AleDelMen/Aquaculture-IoT-device/WebServer/dist/img/boxed-bg.jpg

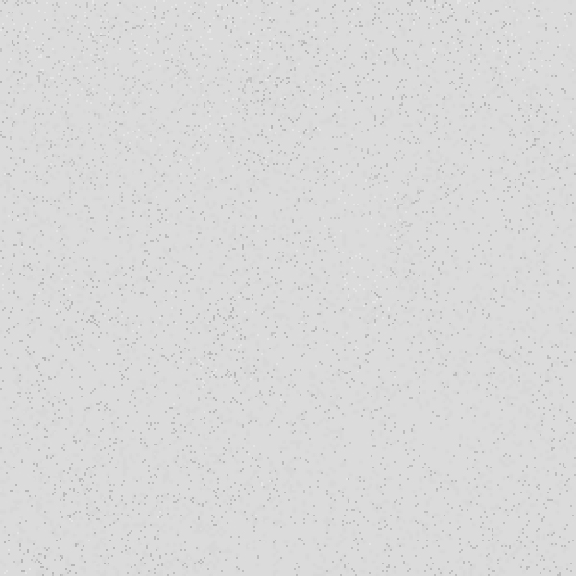
WebServer/dist/img/boxed-bg.jpg
