AleDelMen/Aquaculture-IoT-device/WebServer/dist/img/default-150x150.png

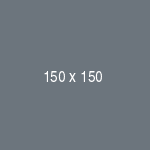
WebServer/dist/img/default-150x150.png
