AleDelMen/Aquaculture-IoT-device/WebServer/dist/img/photo1.png

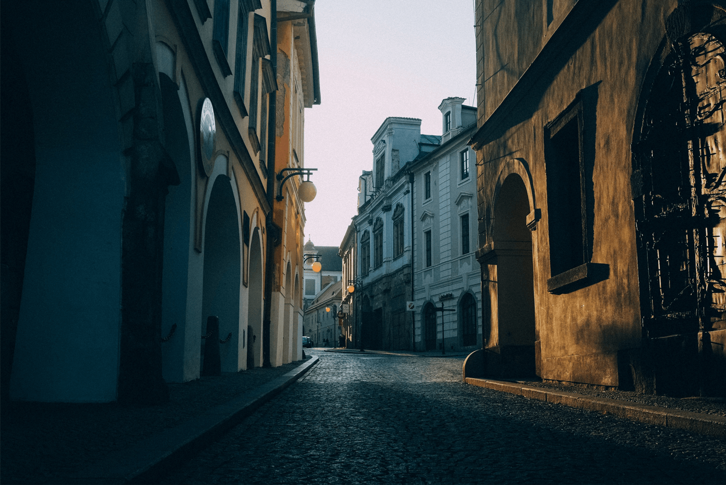
WebServer/dist/img/photo1.png
