AleDelMen/Aquaculture-IoT-device/WebServer/dist/img/photo2.png

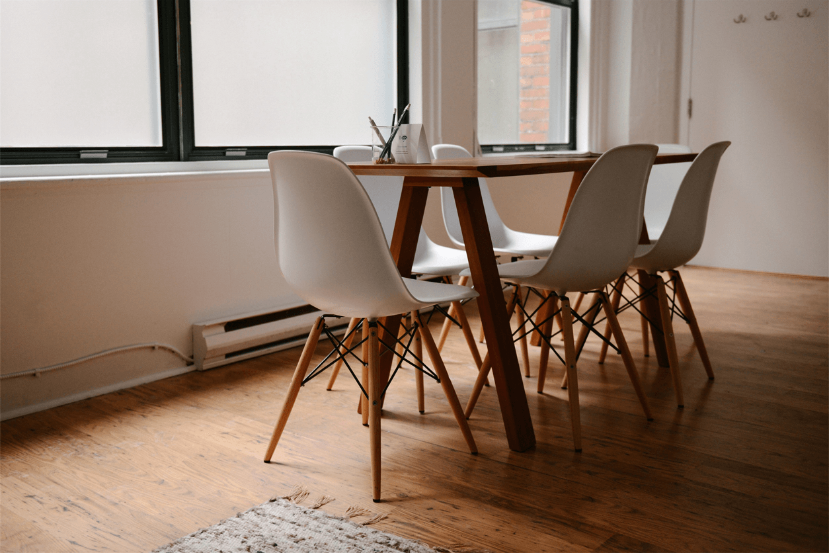
WebServer/dist/img/photo2.png
