AleDelMen/Aquaculture-IoT-device/WebServer/dist/img/photo3.jpg

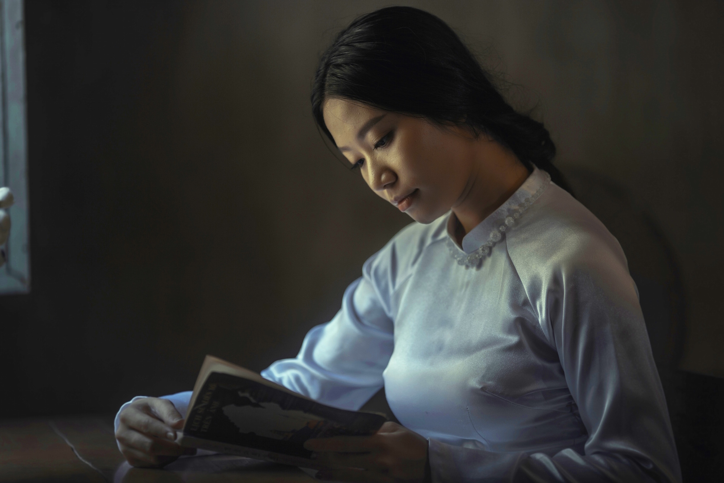
WebServer/dist/img/photo3.jpg
