AleDelMen/Aquaculture-IoT-device/WebServer/dist/img/photo4.jpg

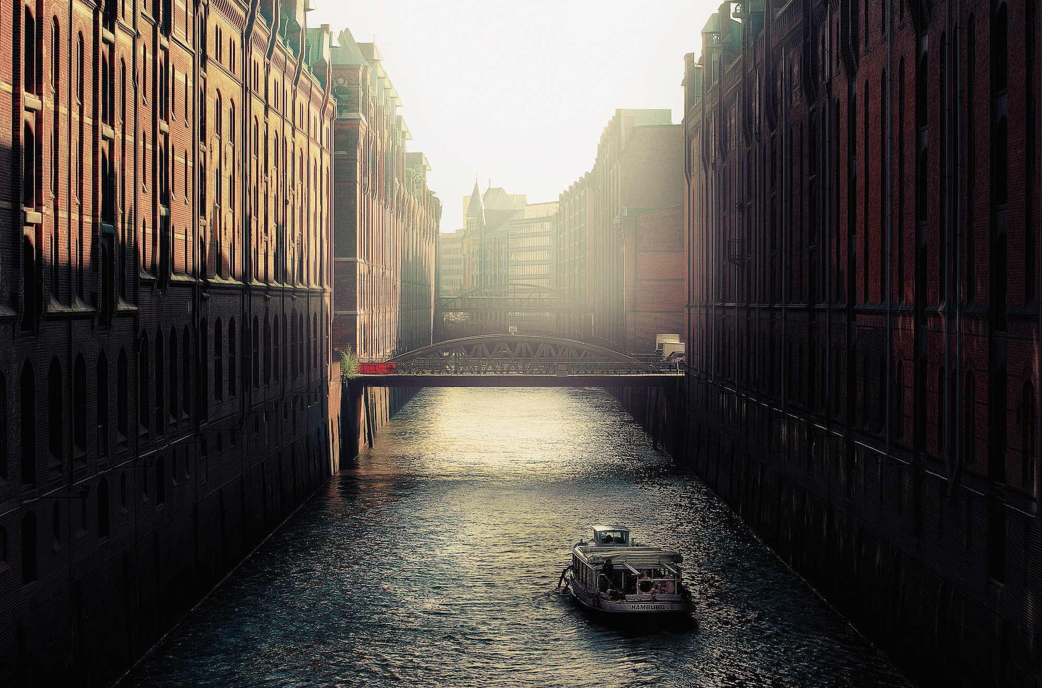
WebServer/dist/img/photo4.jpg
