AleDelMen/Aquaculture-IoT-device/WebServer/dist/img/prod-1.jpg

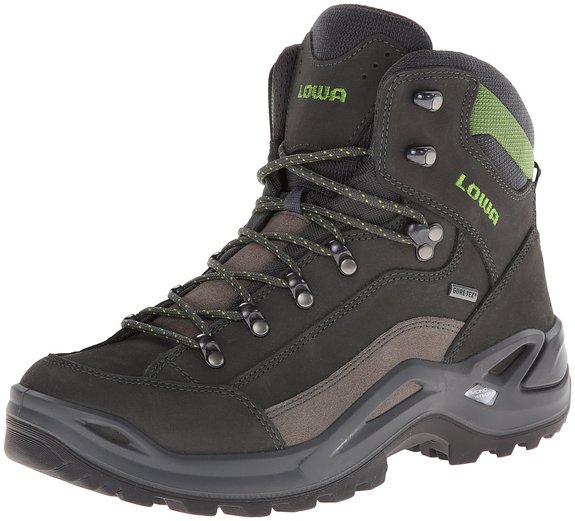
WebServer/dist/img/prod-1.jpg
