AleDelMen/Aquaculture-IoT-device/WebServer/dist/img/prod-2.jpg

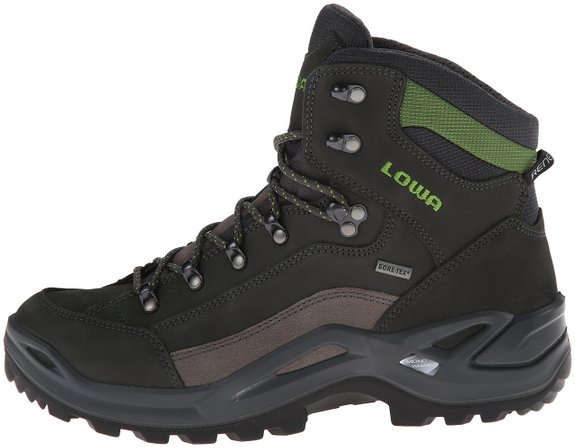
WebServer/dist/img/prod-2.jpg
