AleDelMen/Aquaculture-IoT-device/WebServer/dist/img/prod-3.jpg

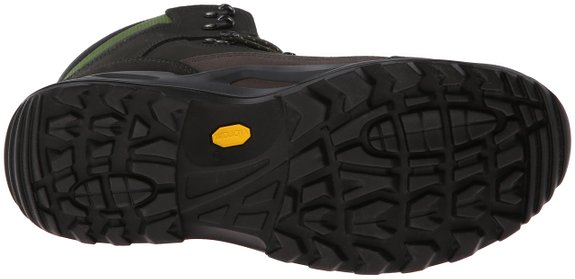
WebServer/dist/img/prod-3.jpg
