AleDelMen/Aquaculture-IoT-device/WebServer/dist/img/prod-4.jpg

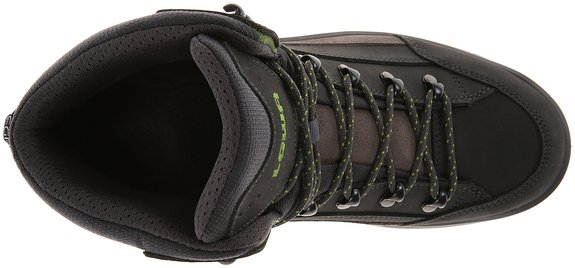
WebServer/dist/img/prod-4.jpg
