AleDelMen/Aquaculture-IoT-device/WebServer/dist/img/prod-5.jpg

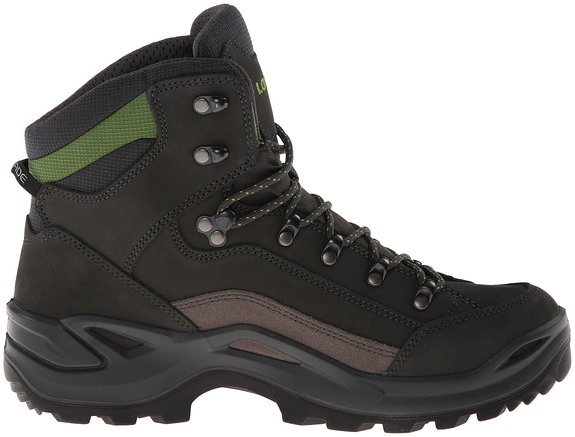
WebServer/dist/img/prod-5.jpg
