AleDelMen/Aquaculture-IoT-device/WebServer/dist/img/user1-128x128.jpg

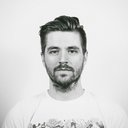
WebServer/dist/img/user1-128x128.jpg
