AleDelMen/Aquaculture-IoT-device/WebServer/dist/img/user2-160x160.jpg

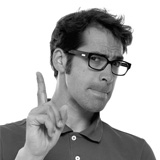
WebServer/dist/img/user2-160x160.jpg
