AleDelMen/Aquaculture-IoT-device/WebServer/dist/img/user3-128x128.jpg

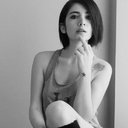
WebServer/dist/img/user3-128x128.jpg
