AleDelMen/Aquaculture-IoT-device/WebServer/dist/img/user4-128x128.jpg

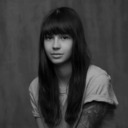
WebServer/dist/img/user4-128x128.jpg
