AleDelMen/Aquaculture-IoT-device/WebServer/dist/img/user5-128x128.jpg

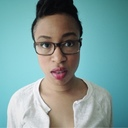
WebServer/dist/img/user5-128x128.jpg
