AleDelMen/Aquaculture-IoT-device/WebServer/dist/img/user6-128x128.jpg

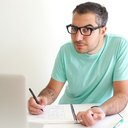
WebServer/dist/img/user6-128x128.jpg
