AleDelMen/Aquaculture-IoT-device/WebServer/dist/img/user7-128x128.jpg

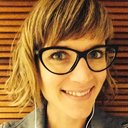
WebServer/dist/img/user7-128x128.jpg
