AleDelMen/Aquaculture-IoT-device/WebServer/dist/img/user8-128x128.jpg

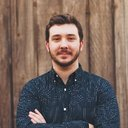
WebServer/dist/img/user8-128x128.jpg
