AleDelMen/Aquaculture-IoT-device/WebServer/img/aqua1.png

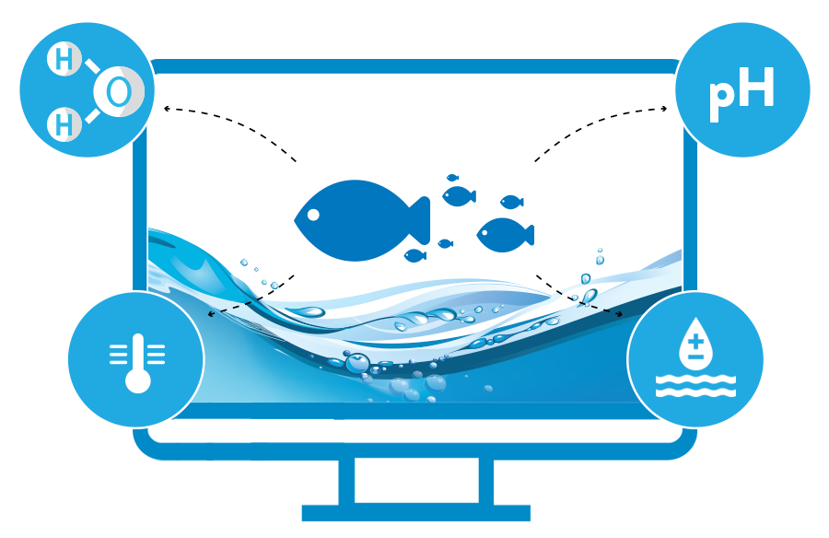
WebServer/img/aqua1.png
