AleDelMen/Aquaculture-IoT-device/WebServer/img/aqua3.png

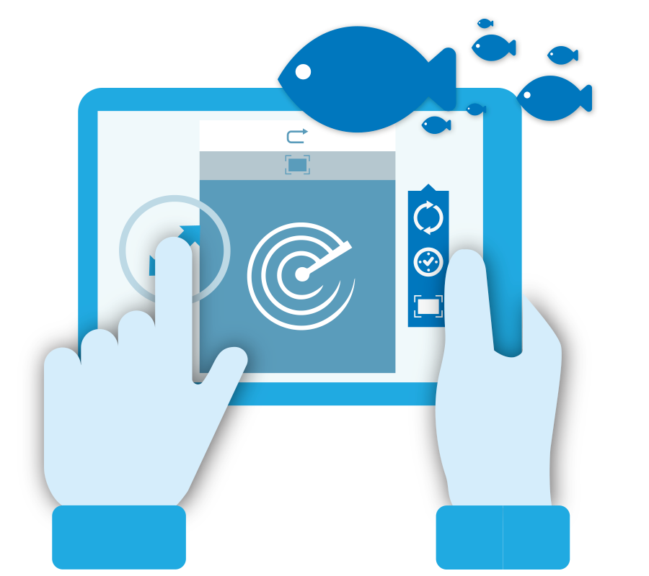
WebServer/img/aqua3.png
