AleDelMen/Aquaculture-IoT-device/WebServer/img/aqua4.png

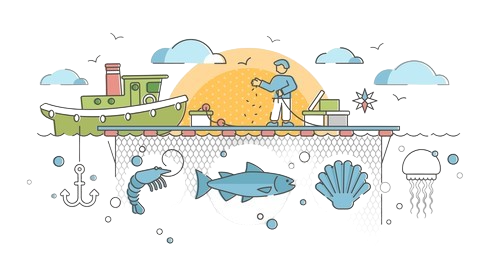
WebServer/img/aqua4.png
