AleDelMen/Aquaculture-IoT-device/WebServer/img/aqua5.png

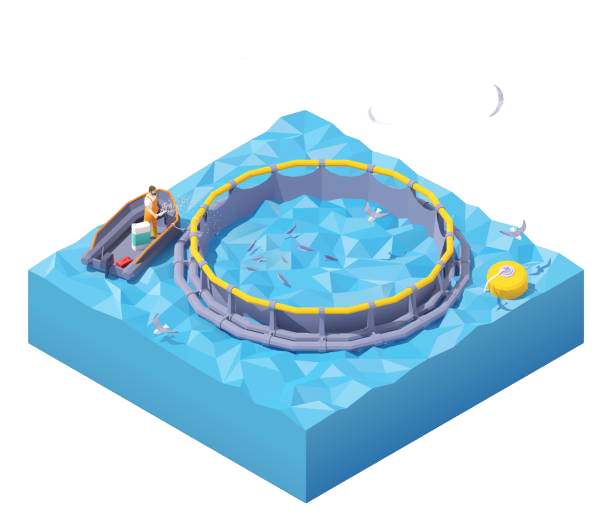
WebServer/img/aqua5.png
