AleDelMen/Aquaculture-IoT-device/WebServer/img/aqua6.jpg

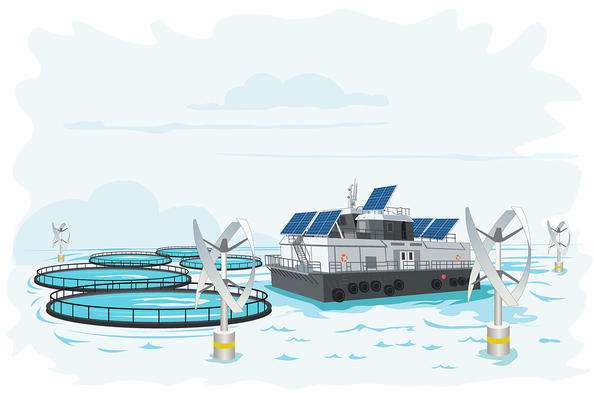
WebServer/img/aqua6.jpg
