AleDelMen/Aquaculture-IoT-device/WebServer/img/Boya_render_2.jpeg

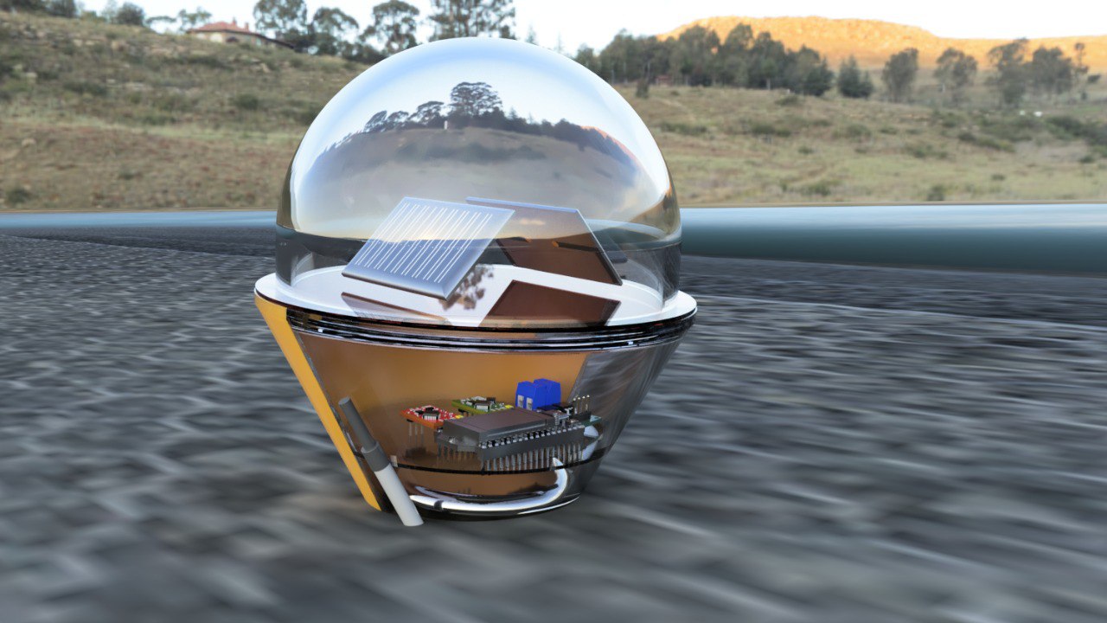
WebServer/img/Boya_render_2.jpeg
