AleDelMen/Aquaculture-IoT-device/WebServer/img/diagrama_sistema.png

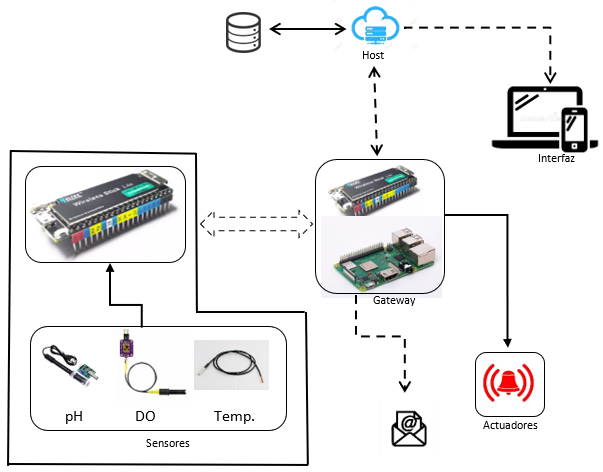
WebServer/img/diagrama_sistema.png
