AleDelMen/Aquaculture-IoT-device/WebServer/img/estanque_ost.png

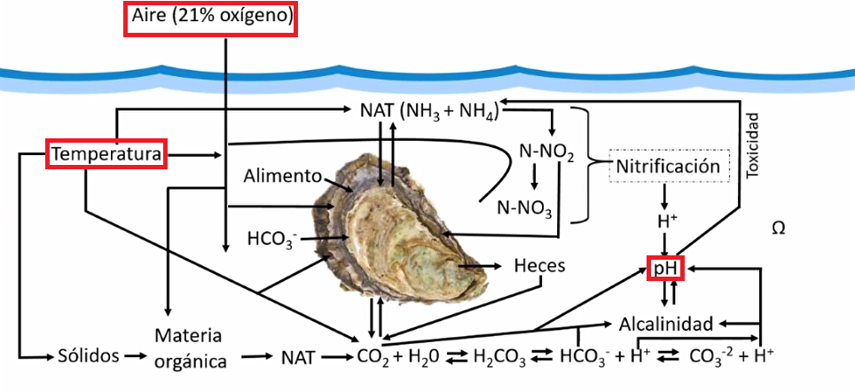
WebServer/img/estanque_ost.png
