AleDelMen/Aquaculture-IoT-device/WebServer/img/fish1.png

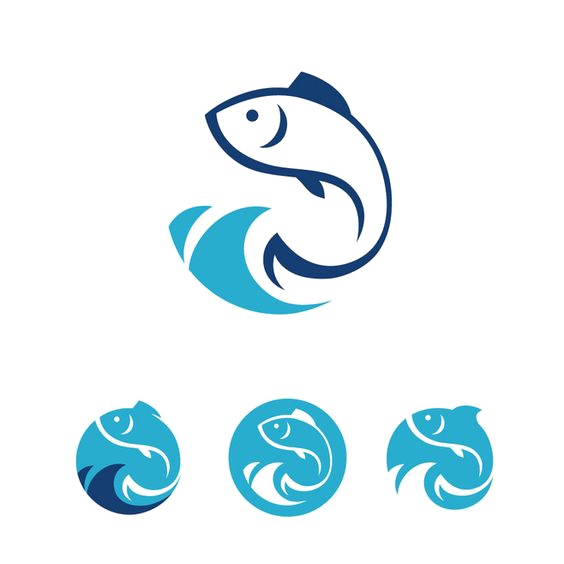
WebServer/img/fish1.png
