AleDelMen/Aquaculture-IoT-device/WebServer/img/fisher1.png

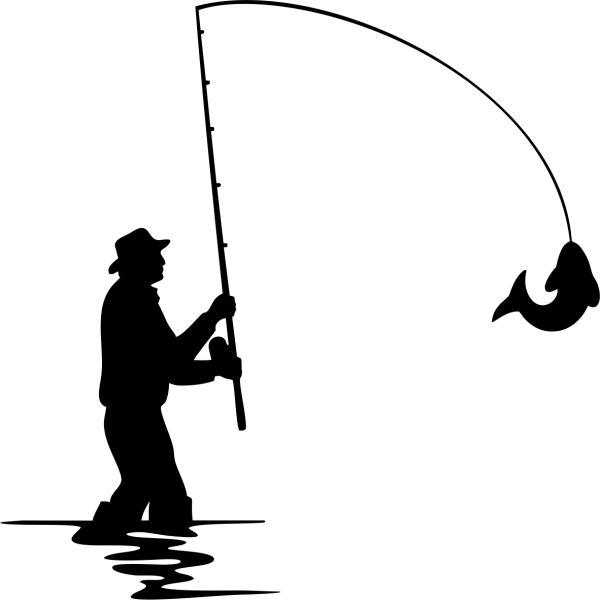
WebServer/img/fisher1.png
