AleDelMen/Aquaculture-IoT-device/WebServer/img/user1.png

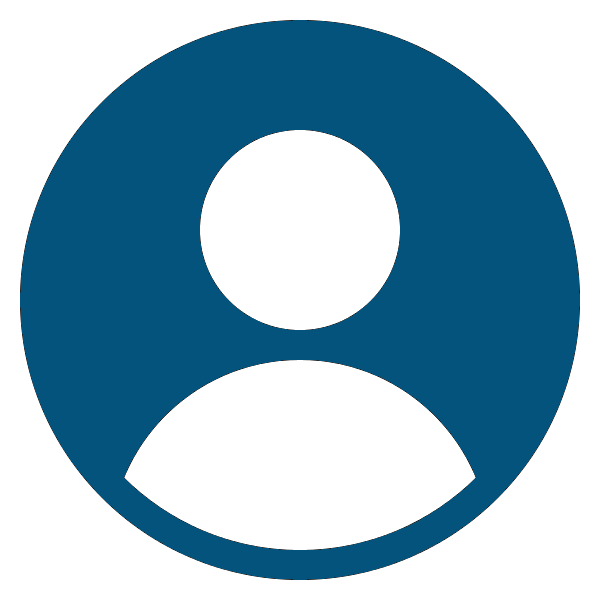
WebServer/img/user1.png
