AleDelMen/Aquaculture-IoT-device/WebServer/img/user2.png

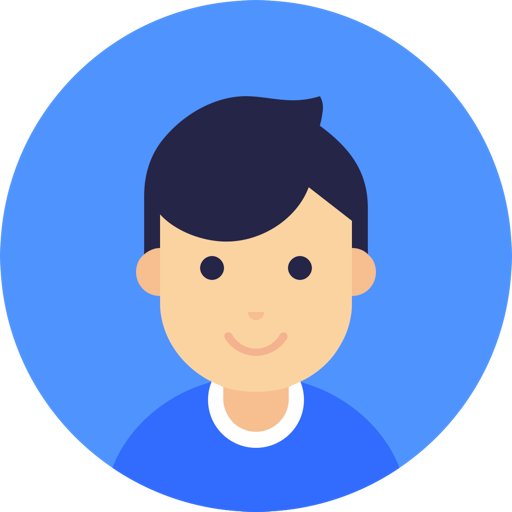
WebServer/img/user2.png
