AleDelMen/Aquaculture-IoT-device/WebServer/img/user3.png

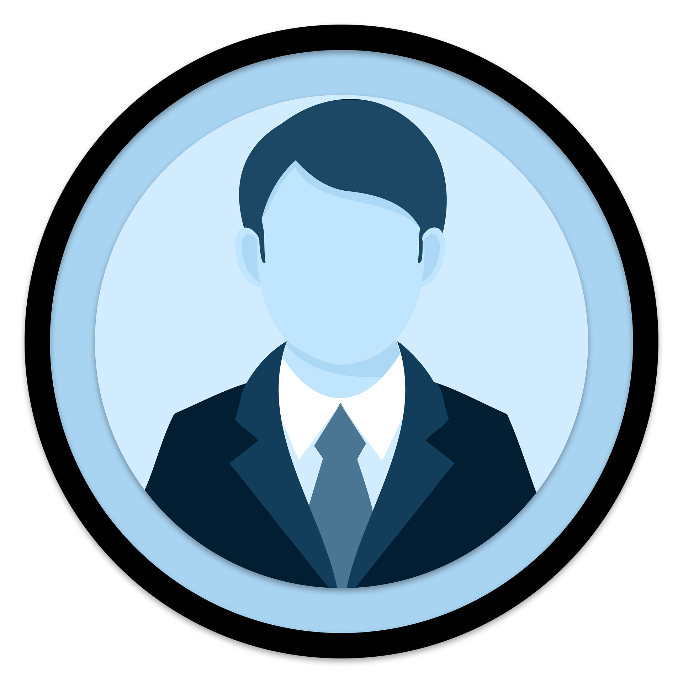
WebServer/img/user3.png
