AleDelMen/Aquaculture-IoT-device/WebServer/img/wave1.png

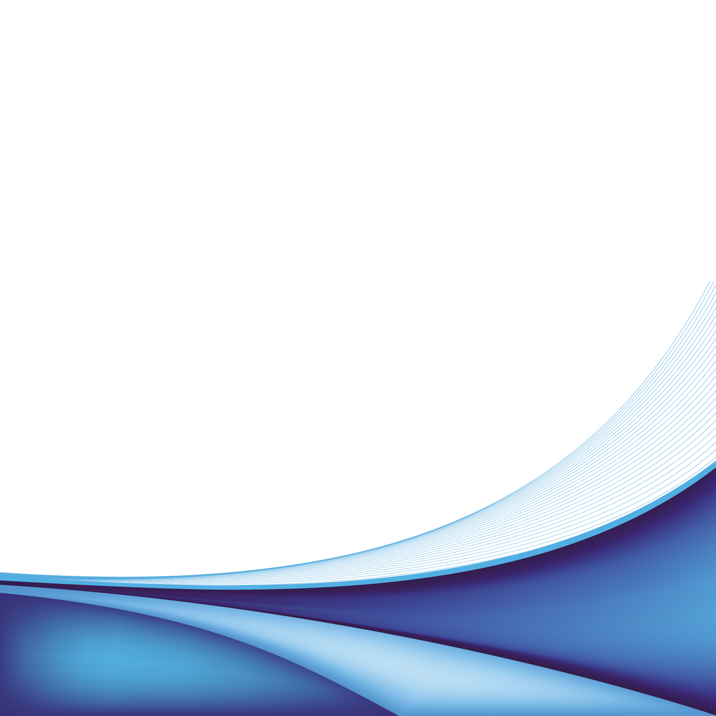
WebServer/img/wave1.png
