AleDelMen/Aquaculture-IoT-device/WebServer/img/wave2.png

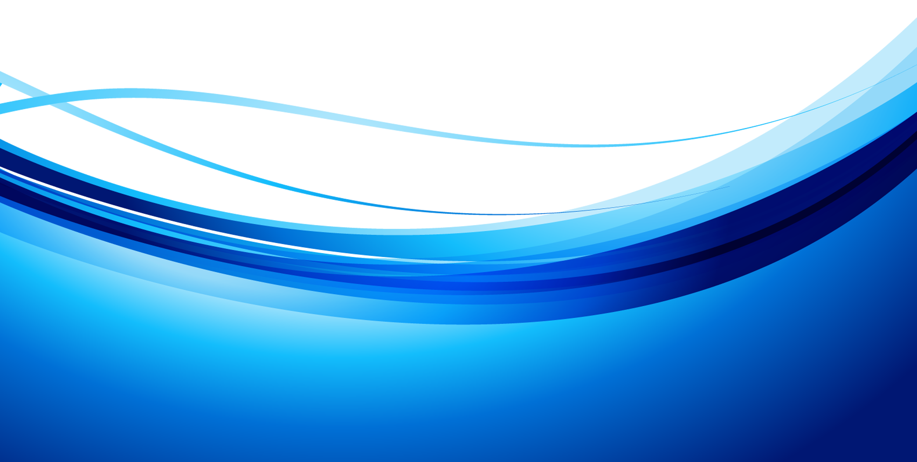
WebServer/img/wave2.png
