AleDelMen/Aquaculture-IoT-device/WebServer/img/wave3.png

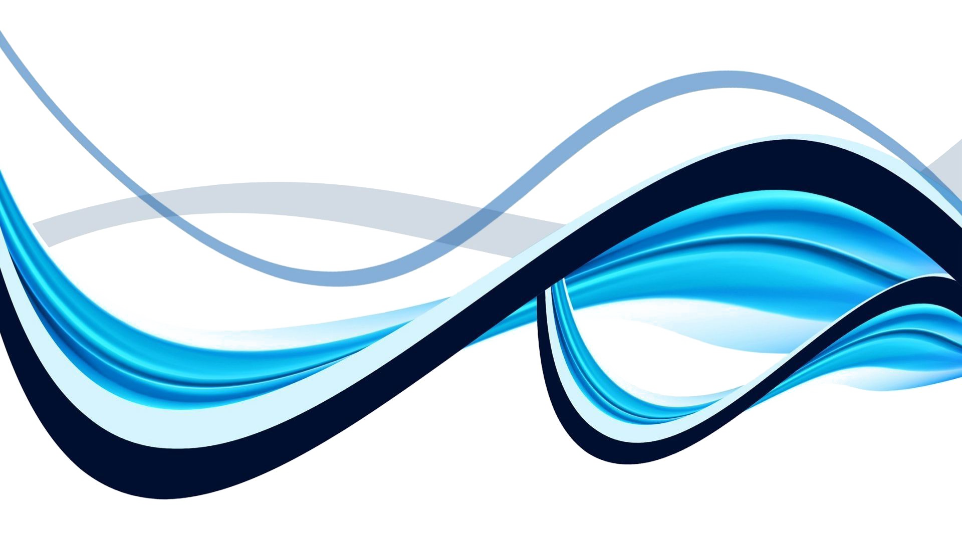
WebServer/img/wave3.png
