AleDelMen/Aquaculture-IoT-device/WebServer/img/wave4.png

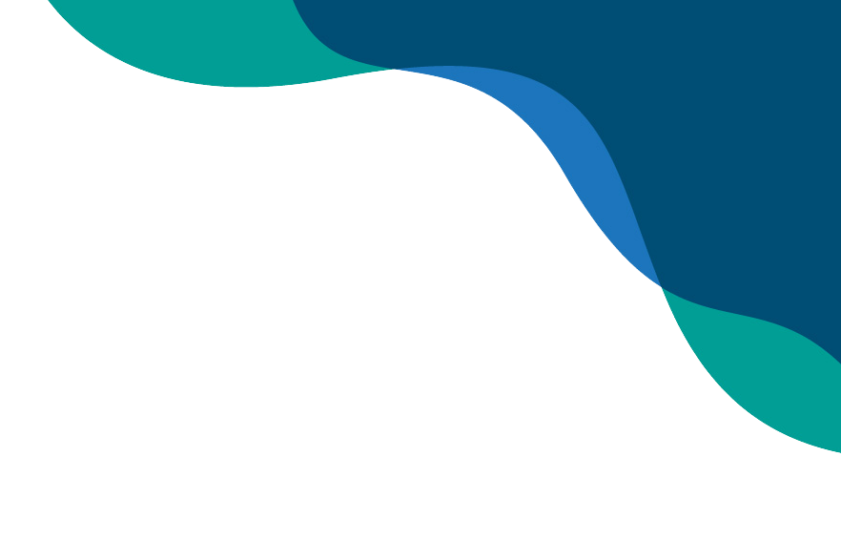
WebServer/img/wave4.png
