AleDelMen/Aquaculture-IoT-device/WebServer/img/wave.png

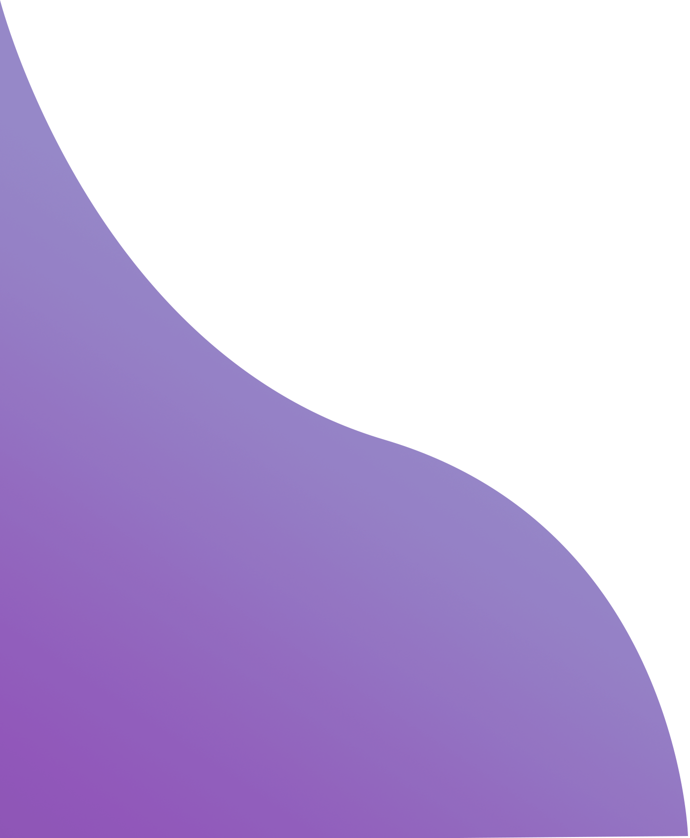
WebServer/img/wave.png
